shimniok/eeZeeMedTiny/documentation/images/20150731112504.jpg

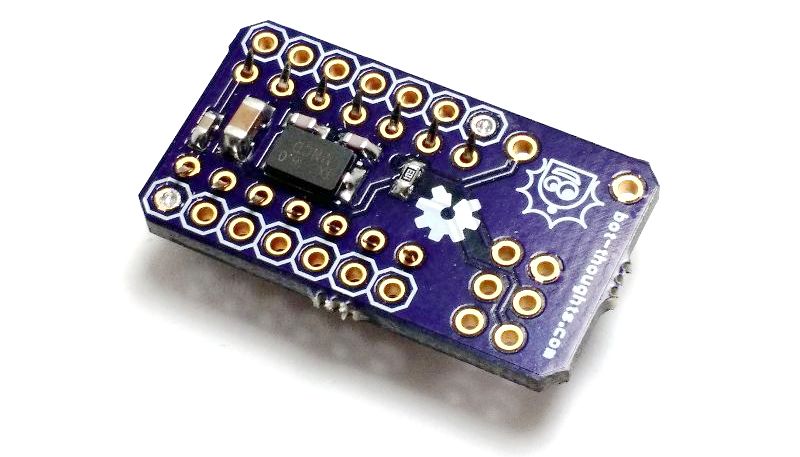
documentation/images/20150731112504.jpg
