shimniok/eeZeeMedTiny/documentation/images/20150731112924.jpg

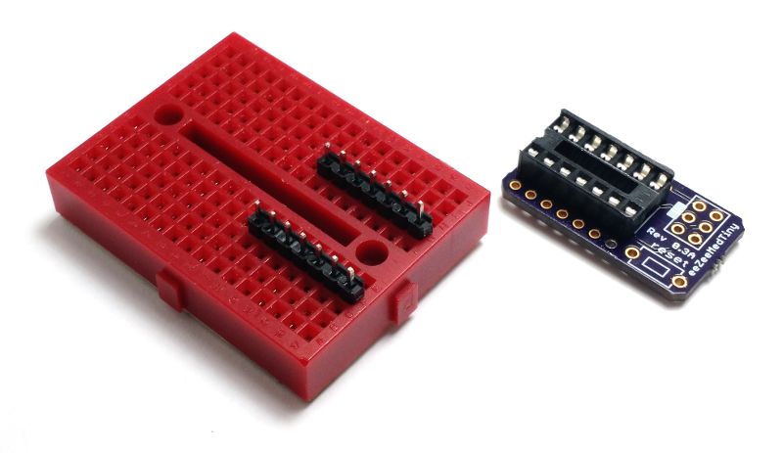
documentation/images/20150731112924.jpg
