shimniok/eeZeeMedTiny/documentation/images/20150731112940.jpg

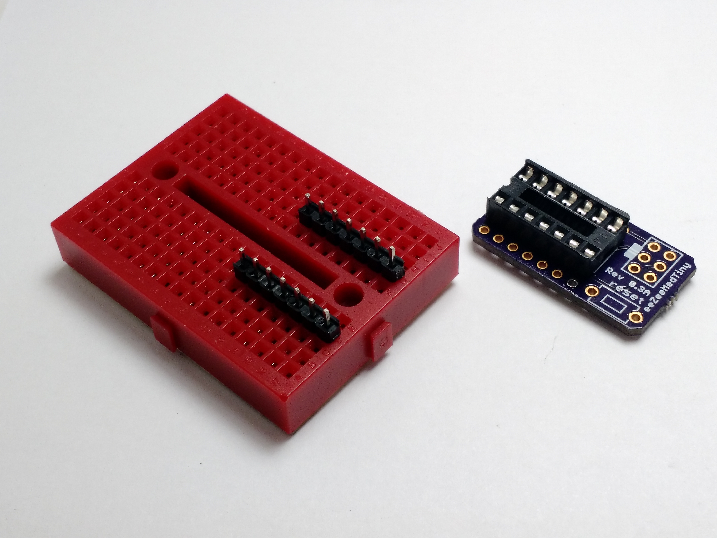
documentation/images/20150731112940.jpg
