shimniok/eeZeeMedTiny/documentation/images/20150731113030.jpg

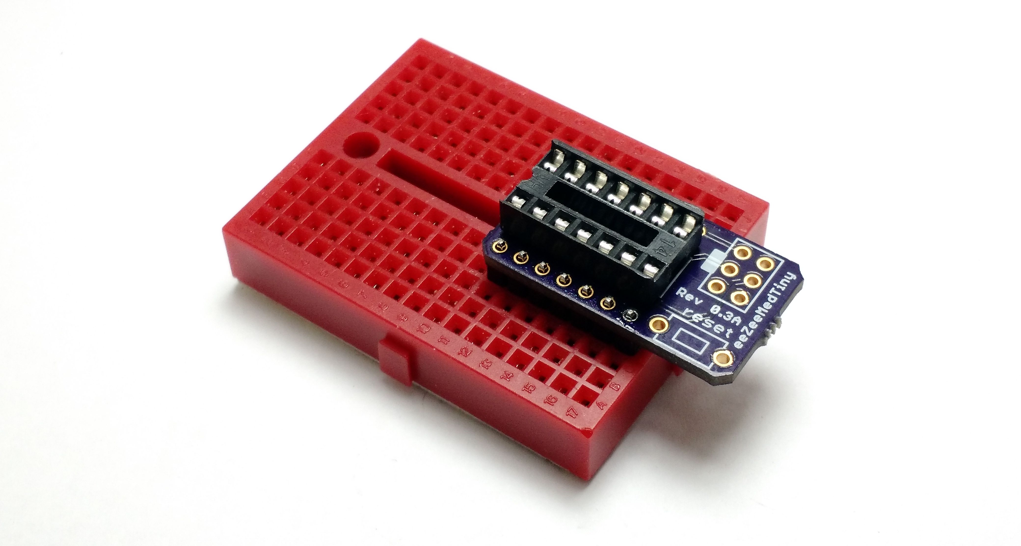
documentation/images/20150731113030.jpg
