shimniok/eeZeeMedTiny/documentation/images/20150731140618.jpg

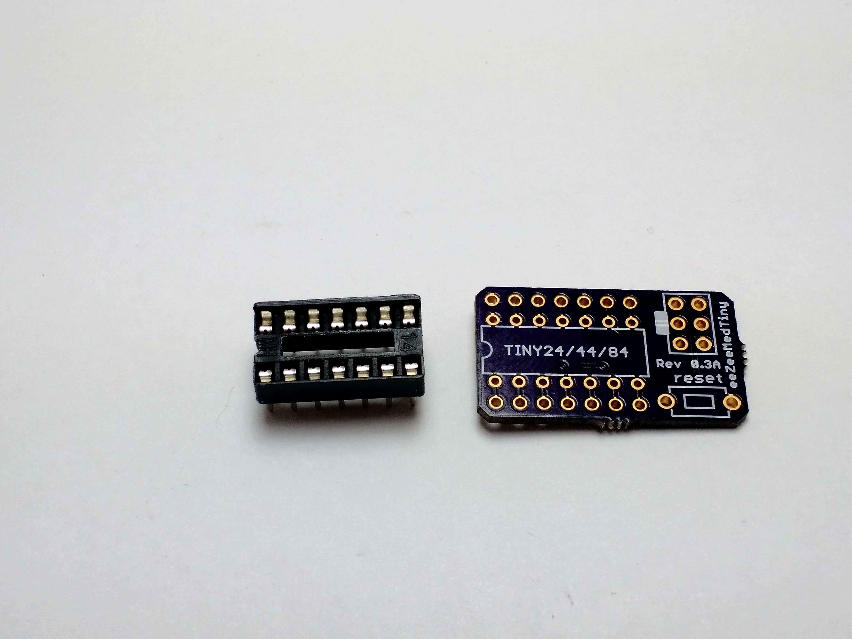
documentation/images/20150731140618.jpg
