shimniok/eeZeeMedTiny/documentation/images/20150731140620.jpg

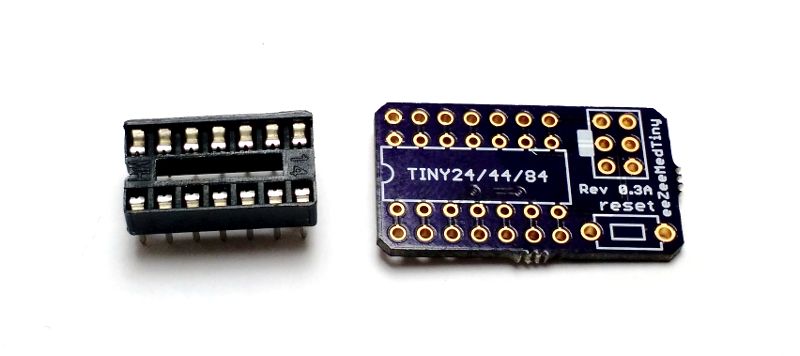
documentation/images/20150731140620.jpg
