shimniok/eeZeeMedTiny/documentation/images/20150731140742.jpg

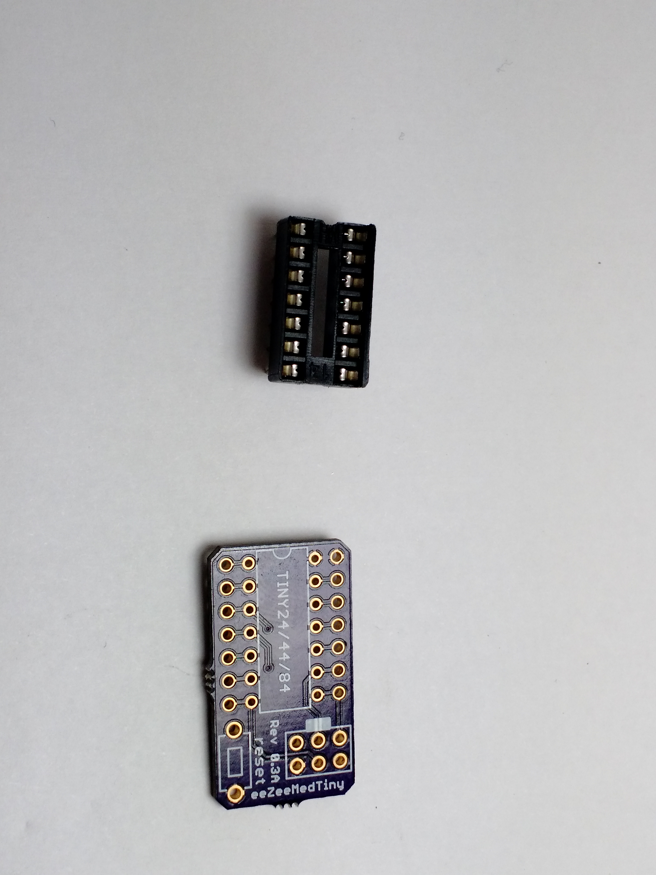
documentation/images/20150731140742.jpg
