shimniok/eeZeeMedTiny/documentation/images/20150731141401.jpg

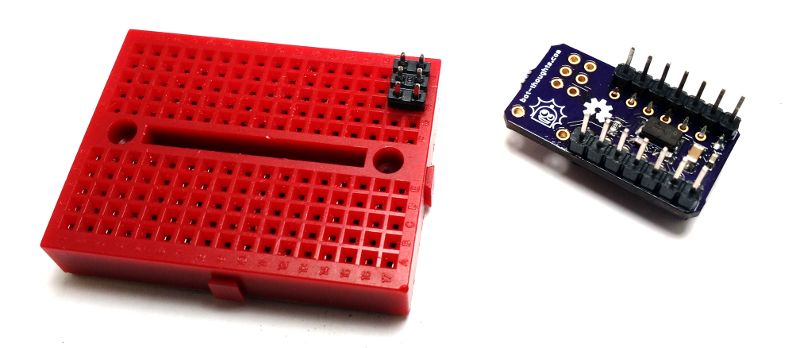
documentation/images/20150731141401.jpg
