shimniok/eeZeeMedTiny/documentation/images/20150731141410.jpg

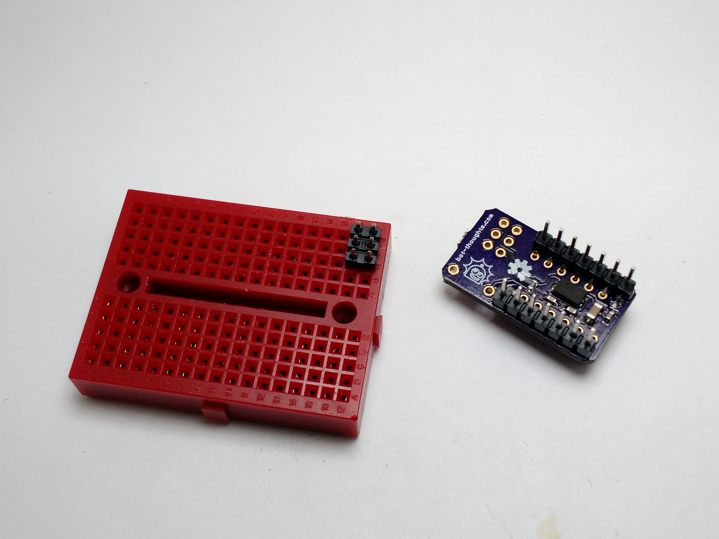
documentation/images/20150731141410.jpg
