shimniok/eeZeeMedTiny/documentation/images/20150731141436.jpg

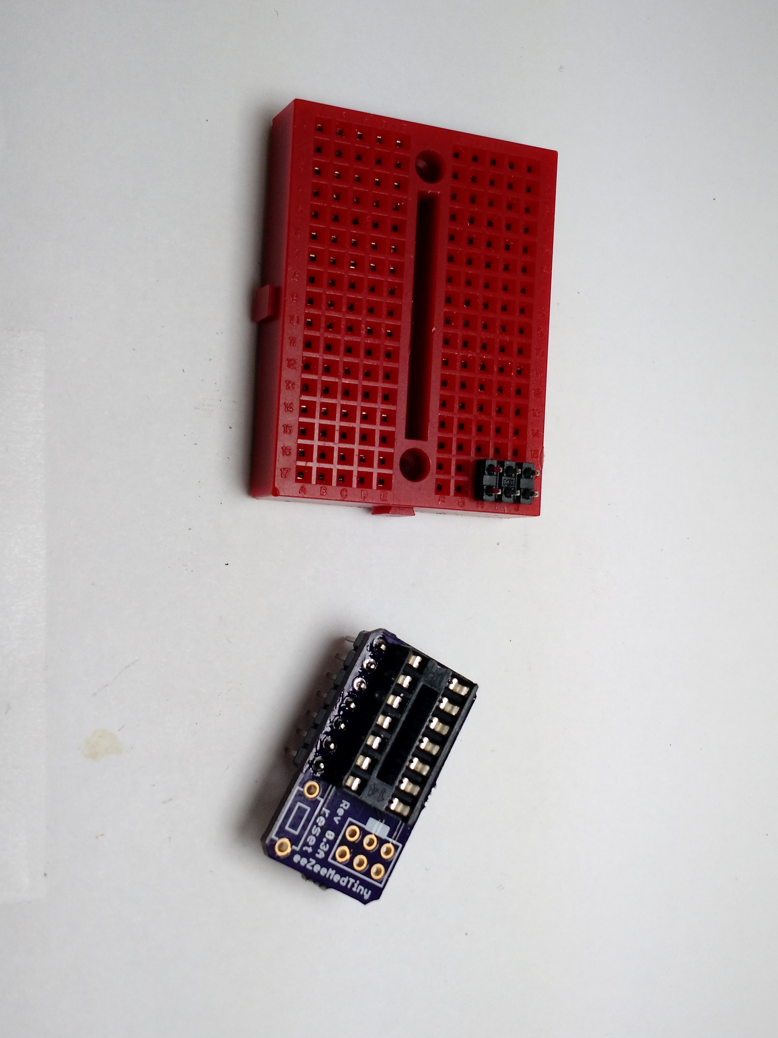
documentation/images/20150731141436.jpg
