shimniok/eeZeeMedTiny/documentation/images/20150731141714.jpg

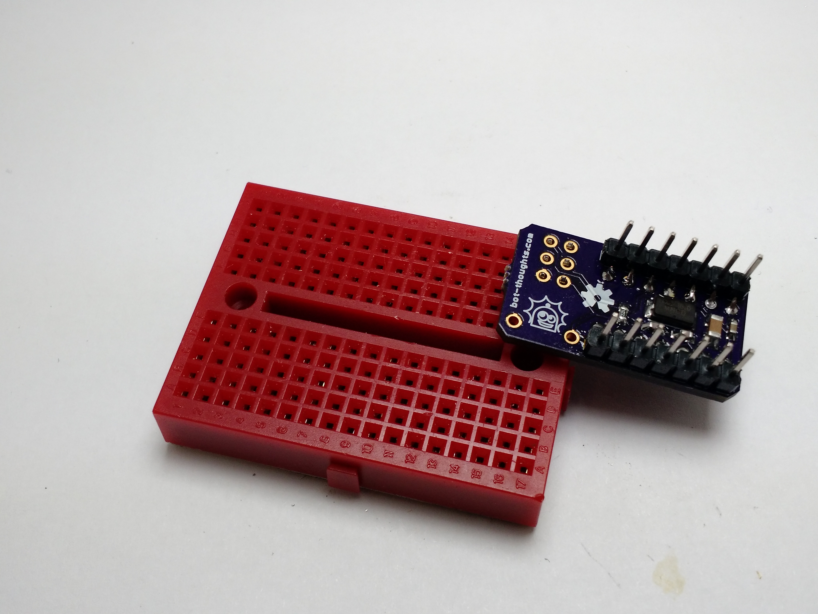
documentation/images/20150731141714.jpg
