shimniok/eeZeeMedTiny/documentation/images/20150731141739.jpg

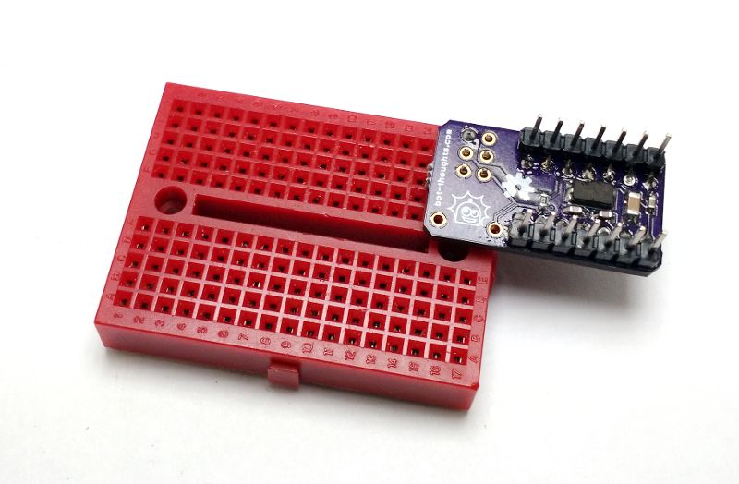
documentation/images/20150731141739.jpg
