shimniok/eeZeeMedTiny/documentation/images/20150731141906.jpg

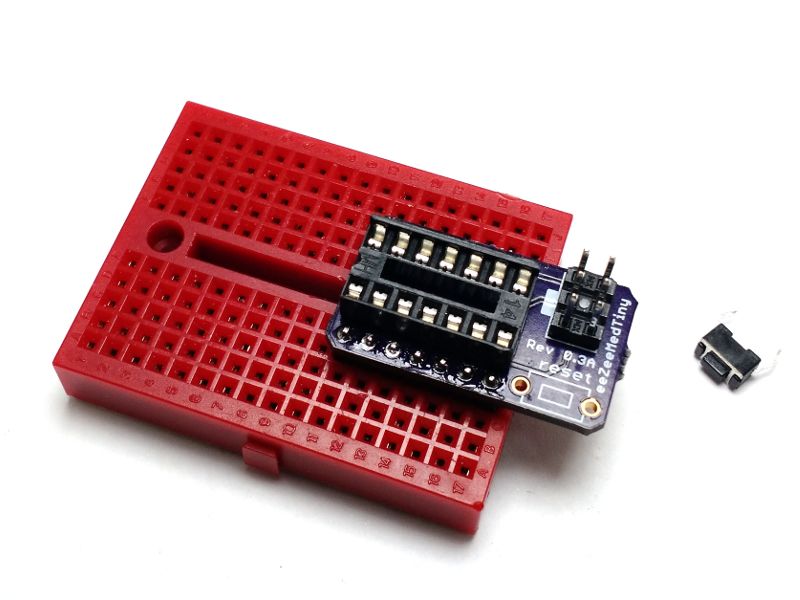
documentation/images/20150731141906.jpg
