shimniok/eeZeeMedTiny/documentation/images/20150731141952.jpg

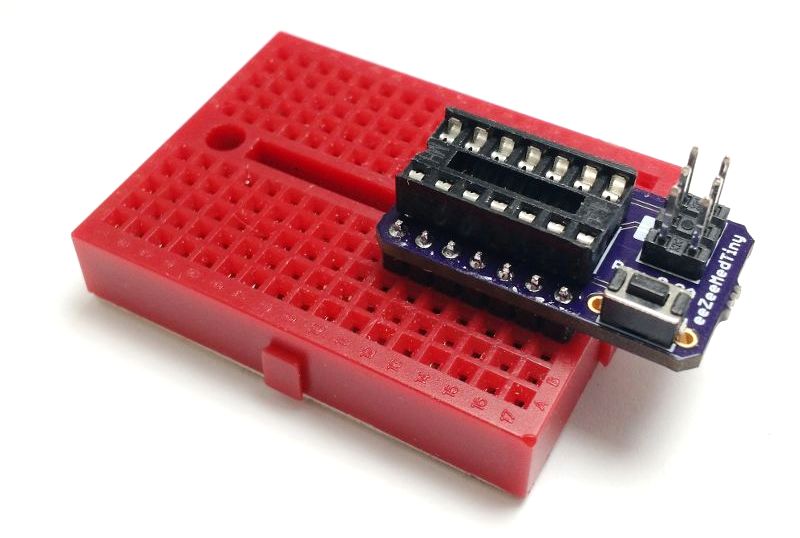
documentation/images/20150731141952.jpg
