shimniok/eeZeeMedTiny/documentation/images/20150731142029.jpg

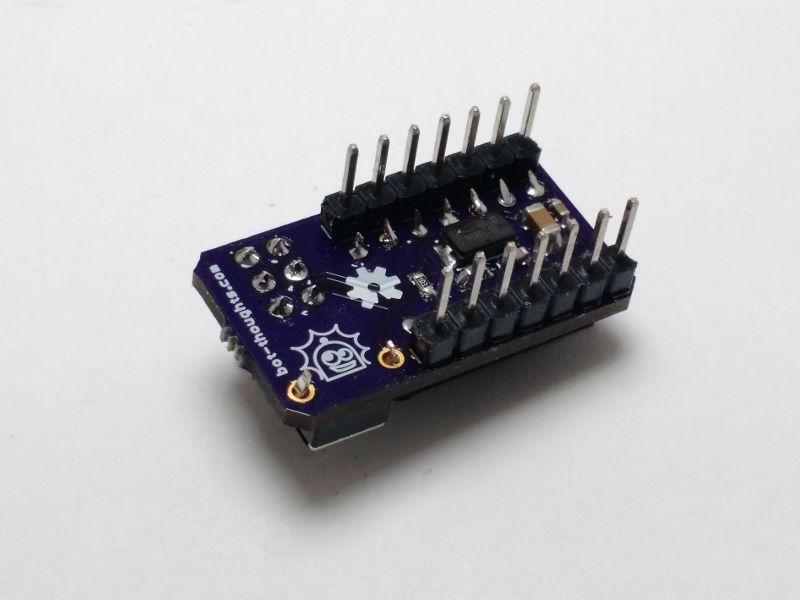
documentation/images/20150731142029.jpg
